adibfarrasy/mera_project/operations_management/Engineering Templates/Test Plan ABC-NN_ _test name_ [Template].xlsx

Clause | NN |  |  | Control
Objective | lorem ipsum dolor sit amet
Test Model | Input
 |  | Input |  | ↓ |  | Output
 | Control
 |  |  | → | Test ABC-NN | →
 | Noise |  |  | ↑
 | Output
 |  |  |  | Noise
Author | John Doe
